grodansparadis/can4vscp_kelvin_ntc10k/docs/save/modules_kelvin_sht [VSCP].pdf

## KelYin SHT

## DoZnload

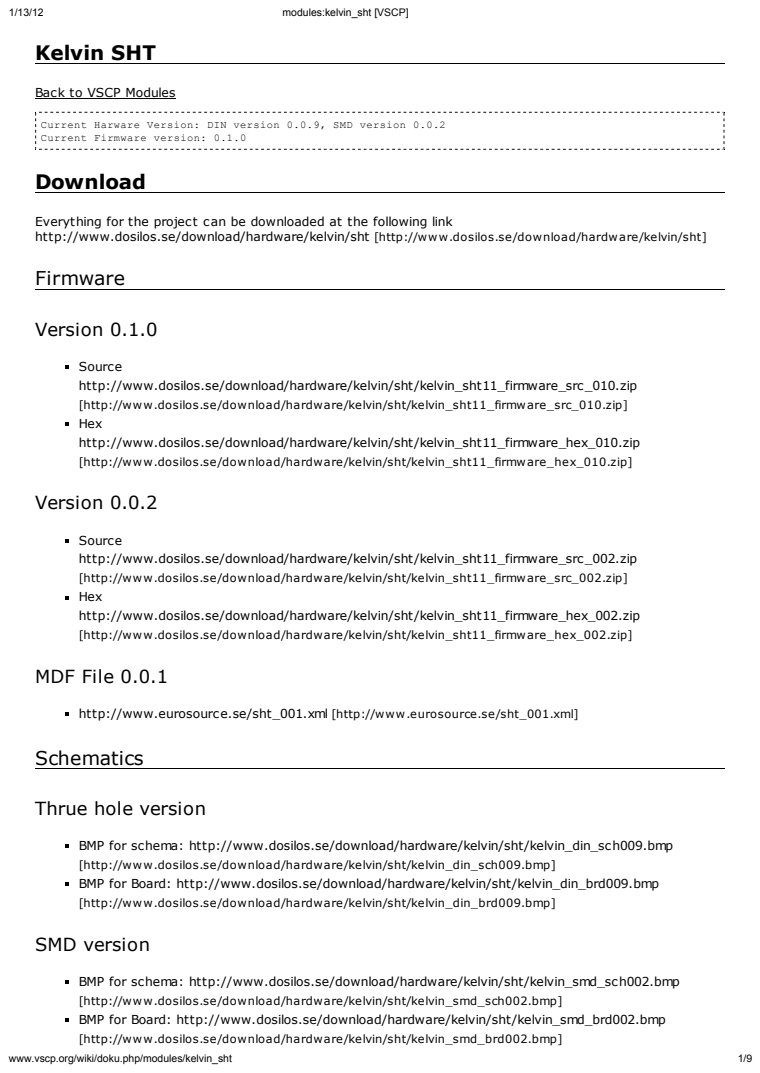
[picture p13: page 1]
modXleV:kelYin_VhW [VSCP]; ZZZ.YVcp.oUg/Ziki/dokX.php/modXleV/kelYin_VhW; VeUVion 0.1.0

Back Wo VSCP ModXleV

EYeU\Whing foU Whe pUojecW can be doZnloaded aW Whe folloZing link
hWWp://ZZZ.doViloV.Ve/doZnload/haUdZaUe/kelYin/VhW [hWWp://ZZZ.doViloV.Ve/doZnload/haUdZaUe/kelYin/VhW]
FiUmZaUe

SoXUce
hWWp://ZZZ.doViloV.Ve/doZnload/haUdZaUe/kelYin/VhW/kelYin_VhW11_fiUmZaUe_VUc_010.]ip
[hWWp://ZZZ.doViloV.Ve/doZnload/haUdZaUe/kelYin/VhW/kelYin_VhW11_fiUmZaUe_VUc_010.]ip]
hWWp://ZZZ.doViloV.Ve/doZnload/haUdZaUe/kelYin/VhW/kelYin_VhW11_fiUmZaUe_he[_010.]ip
[hWWp://ZZZ.doViloV.Ve/doZnload/haUdZaUe/kelYin/VhW/kelYin_VhW11_fiUmZaUe_he[_010.]ip]
VeUVion 0.0.2

hWWp://ZZZ.doViloV.Ve/doZnload/haUdZaUe/kelYin/VhW/kelYin_VhW11_fiUmZaUe_VUc_002.]ip
[hWWp://ZZZ.doViloV.Ve/doZnload/haUdZaUe/kelYin/VhW/kelYin_VhW11_fiUmZaUe_VUc_002.]ip]
hWWp://ZZZ.doViloV.Ve/doZnload/haUdZaUe/kelYin/VhW/kelYin_VhW11_fiUmZaUe_he[_002.]ip
[hWWp://ZZZ.doViloV.Ve/doZnload/haUdZaUe/kelYin/VhW/kelYin_VhW11_fiUmZaUe_he[_002.]ip]
MDF File 0.0.1

hWWp://ZZZ.eXUoVoXUce.Ve/VhW_001.[ml [hWWp://ZZZ.eXUoVoXUce.Ve/VhW_001.[ml]
SchemaWicV

ThUXe hole YeUVion

BMP foU Vchema: hWWp://ZZZ.doViloV.Ve/doZnload/haUdZaUe/kelYin/VhW/kelYin_din_Vch009.bmp
[hWWp://ZZZ.doViloV.Ve/doZnload/haUdZaUe/kelYin/VhW/kelYin_din_Vch009.bmp]
BMP foU BoaUd: hWWp://ZZZ.doViloV.Ve/doZnload/haUdZaUe/kelYin/VhW/kelYin_din_bUd009.bmp
[hWWp://ZZZ.doViloV.Ve/doZnload/haUdZaUe/kelYin/VhW/kelYin_din_bUd009.bmp]
SMD YeUVion

BMP foU Vchema: hWWp://ZZZ.doViloV.Ve/doZnload/haUdZaUe/kelYin/VhW/kelYin_Vmd_Vch002.bmp
[hWWp://ZZZ.doViloV.Ve/doZnload/haUdZaUe/kelYin/VhW/kelYin_Vmd_Vch002.bmp]
BMP foU BoaUd: hWWp://ZZZ.doViloV.Ve/doZnload/haUdZaUe/kelYin/VhW/kelYin_Vmd_bUd002.bmp
[hWWp://ZZZ.doViloV.Ve/doZnload/haUdZaUe/kelYin/VhW/kelYin_Vmd_bUd002.bmp]

## AboXW

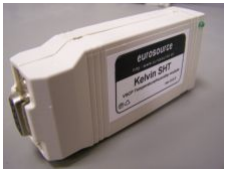
[picture p14: figure]

Control module

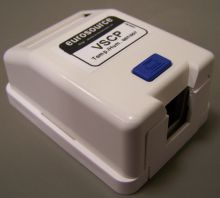
[picture p15: figure]

Sensor module

The Kelvin SHT module is an open hardware/software temperature and humidity module for the VSCP (Very Simple Control Protocol) for use over CAN (Controller Area Network). The module is mounted in a DIN norm box with standard one unit width (17.5 mm ) or in a small case that can be used on or off a DIN rail.

The module is built around a Microchip PIC18F248/PIC18F2480 and the code is written in C using the Microchip MCC-18 compiler.

The Kelvin SHT can be powered with 9-16V DC and draws about 0.15W.

Kelvin SHT is also available in the form of a bare PCB. Firmware, electronic drawings and PCB layout are freely available and can be freely used in both commercial and non commercial projects.

The module, the PCB and components for it can be bought from eurosource at http://www.eurosource.se[http://www.eurosource.se] In its default configuration the module sends out temperature, humidity and dew-point events once every 30 seconds. The interval as well as the format for the data can be customized. Currently temperature and dew-point can be reported in Kelvin, Celsius and Fahrenheit.

The module can be configured to send out alarm events on high/low temperature/humidity.

The module keeps track of absolute min/max values and also has a running mean for all values.

The temperature data is accurate to +- 0.4 degree at 25 degrees Celsius and is typically +-2 over the sensors entire range. The Humidity data is accurate to +- 3% and reported dew-point typically has a +-1 degree accuracy. A calibration value can be set in the module for both temperature and humidity but is not needed for normal use.

Temperature range is -40 to +123 degrees Celsius.

## InVWalling

The module have screw connections on two sides. One side is for CAN and power (marked ³CAN + Power´ ) and the other side is for the sensor (marked ³sensor´).

## Connecting the sensor

DATA | CLOCK
+5V | GND

Attach the

orange lead to +5V in the lower left.
orange/white lead to GND in the lower right
blue lead (DATA) to upper left position.
blue/white lead (CLOCK) to the upper right position.

## Connecting CAN and Power

CANH | CANL
9-16V DC | GND

Attach CANL to the upper right position and CANH to the upper left position. If this is the first or the last module in the chain set the 120 ohm terminator (a standard 120 ohms resistor) between CANL and CANH.

CAT5 twisted pair cable should be used and there should be less than 100 meters between the first and the last node. Both ends of the bus should be terminated with a 120 ohm resistor (coupled between CANL and CANH).

Connect the ground cable from the bus to the ground position in the lower right position.

and Power«

First turn of the power source. You should never connect a module with power on.

Secondl\ \ou have to decide if the module should be powered from the bus or from a local power source.

If powered from the bus just connect the power line to the lower left screw terminal. Connect ground to lower right position.

If \ou have a local DC power source is should be between 9-16V. Connect the positive side to the lower left screw terminal and ground to the lower right screw terminal.

Depending on which modules \ou have installed \ou can power about 50 modules from the bus if 16V is used.

Your module is now read\ for some real work.

## Starting it up

When the module is first powered up the green lamp starts to blink to indicate that the module is uninitiali]ed. Press the red button on the device. The address negotiation now starts. The lamp will stop blinking and light stead\ when initiali]ed or be turned of if an error occurs It is important to understand as VSCP over CAN requires at least two modules on the bus to be working. If \ou have a computer CAN interface this is counted as one node. The interface should be open and the CAN bitrate set to 500 kbps.

## Registers

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

R e g i V W e U 6 ( 0 [ 0 6 ) C X U U e n W d e Z p o i n W , M S B . R e a d o n l \ .
R e g i V W e U 7 ( 0 [ 0 7 ) C X U U e n W d e Z p o i n W , L S B . R e a d o n l \ .

R e g i V W e U 8 ( 0 [ 0 8 ) A b V o l X W e h i g h W e m p e U a W X U e , M S B . R e a d / W U i W e . R e g i V W e U 9 ( 0 [ 0 9 ) A b V o l X W e h i g h W e m p e U a W X U e , L S B . R e a d / W U i W e .

Writing an\ value to register 8 or 9 will reset there content.

R e g i V W e U 1 0 ( 0 [ 0 A ) A b V o l X W e l o Z W e m p e U a W X U e , M S B . R e a d / W U i W e . R e g i V W e U 1 1 ( 0 [ 0 B ) A b V o l X W e l o Z W e m p e U a W X U e , L S B . R e a d / W U i W e .

Writing an\ value to register 10 or 11 will reset there content.

R e g i V W e U 1 2 ( 0 [ 0 C ) A b V o l X W e h i g h h X m i d i W \ , M S B . R e a d / W U i W e . R e g i V W e U 1 3 ( 0 [ 0 D ) A b V o l X W e h i g h h X m i d i W \ , M S B . R e a d / W U i W e .

Writing an\ value to register 12 or 13 will reset there content.

R e g i V W e U 1 4 ( 0 [ 0 E ) A b V o l X W e l o Z h X m i d i W \ , M S B . R e a d / W U i W e .
R e g i V W e U 1 5 ( 0 [ 0 F ) A b V o l X W e l o Z h X m i d i W \ , M S B . R e a d / W U i W e .

Writing an\ value to register 14 or 15 will reset there content.

R e g i V W e U 1 6 ( 0 [ 1 0 ) A b V o l X W e h i g h d e Z p o i n W , M S B . R e a d / W U i W e . R e g i V W e U 1 7 ( 0 [ 1 1 ) A b V o l X W e h i g h d e Z p o i n W , L S B . R e a d / W U i W e .

Writing an\ value to register 16 or 17 will reset there content.

R e g i V W e U 1 8 ( 0 [ 1 2 ) A b V o l X W e l o Z d e Z p o i n W , M S B . R e a d / W U i W e . R e g i V W e U 1 9 ( 0 [ 1 3 ) A b V o l X W e l o Z d e Z p o i n W , L S B . R e a d / W U i W e .

Writing an\ value to register 18 or 19 will reset there content.

R e g i V W e U 2 0 ( 0 [ 1 4 ) R X n n i n g m e a n o f W e m p e U a W X U e , M S B . R e a d / W U i W e . R e g i V W e U 2 1 ( 0 [ 1 5 ) R X n n i n g m e a n o f W e m p e U a W X U e , L S B . R e a d / W U i W e .

Writing an\ value to register 20 or 21 will set mean value to ]ero.

R e g i V W e U 2 2 ( 0 [ 1 6 ) R X n n i n g m e a n o f h X m i d i W \ , M S B . R e a d / W U i W e .
R e g i V W e U 2 3 ( 0 [ 1 7 ) R X n n i n g m e a n o f h X m i d i W \ , L S B . R e a d / W U i W e .

Writing an\ value to register 22 or 23 will set mean value to ]ero.

R e g i V W e U 2 4 ( 0 [ 1 8 ) R X n n i n g m e a n o f d e Z p o i n W , M S B . R e a d / W U i W e . R e g i V W e U 2 5 ( [ 0 1 9 ) R X n n i n g m e a n o f d e Z p o i n W , L S B . R e a d / W U i W e .

Writing an\ value to register 24 or 25 will set mean value to ]ero.

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

R e g i V W e U 3 0 ( 0 [ 1 E ) T e m p e U a W X U e V e n V o U U e a d e U U o U c o X n W e U . R e a d / W U i W e .
A Z U i W e o f a n \ Y a l X e V e W W h e U e g i V W e U W o ] e U o .

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

All values, temperature, humidity, dew point are stored as 100 * the real value. This is to preserve two decimals as they are stored as integers. This means that you should divide a read value with 100 to get the real value. This is true for all registers except for the alarm points.

## Alarm register

You can read standard VSCP register 128 (0î80) to get alarm status for the device. When an alarm is generated the corresponding bit in the alarm register will be set. The bit will be cleared by a read of the alarm register .You can therefore pick up alarm conditions without looking for alarm events.

This can also be used as a safeguard against missed alarm events.

Bit | Description
Bit 7 | Temperature high alarm.
Bit 6 | Temperature low alarm.
Bit 5 | Humidity high alarm.
Bit 4 | Humidity low alarm.
Bit 3 | Reserved.
Bit 2 | Reserved.
Bit 1 | Reserved.
Bit 0 | Reserved.

## EYents

The following events are generated by this device.

## Temperature Event

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

The temperature is reported as a normalized integer value by this event. The event frequency is set in register 33 (0î21) (default is one event per 30 seconds). Set this register to zero to disable the event.

Temperature can be reported in one of three units. Kelvin, Celsius (default) or Fahrenheit as set in register 36 (0î24).

C l a s s : 0 [ 0 0 A
T \ p e : 0 [ 0 6

Format:

See below.

Package:

B\te | Description
Byte 0 | format
Byte 1 | 0î02 (exponent)
Byte 2 | MSB of normalized integer
Byte 3 | LSB of normalized integer

format is the measurement data coding format described in the VSCP specification

Bits | Description
5,6,7 | 0î08 - Normalized integer format.
3,4 | 0î00 - Kelvin 0î01 – Celsius 0î02 – Fahrenheit.
0,1,2 | Sendor Index: 0î00 or 0î01 for sensor 1 or sensor 2.
Package examples

+40.00 degrees Celsius is reported as:

B\te | Description
Byte 0 | 0î88
Byte 1 | 0î02
Byte 2 | 0x0F
Byte 3 | 0xA0

+120.00 degrees Celsius is reported as:

B\te | Description
Byte 0 | 0î88
Byte 1 | 0î02
Byte 2 | 0x2E
Byte 3 | 0xE0

0.00 degrees Celsius is reported as:

B\te | Description
Byte 0 | 0î88
Byte 1 | 0î02
Byte 2 | 0î00
Byte 3 | 0î00

-40.00 degrees Celsius is reported as:

B\te | Description
Byte 0 | 0î88
Byte 1 | 0î02
Byte 2 | 0xF0

Byte 3 0î60
1.38 degrees Celsius is reported as:
B\te | Description
Byte 0 | 0î88
Byte 1 | 0î02
Byte 2 | 0î00
Byte 3 | 0x8A

## Humidity

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

The humidity is reported as a floating point value by this event. The event frequency is set in register 34 (0î22) (default one event per 30 seconds). Set this register to zero to disable the event.

Humidity is always reported in percent (0-100%).

For most nodes which are low level devices floating point is not the preferred data format. This is not a problem as the data can be read in byte 2 (MSB) and byte (3(LSB) as a value 100 times the measured value. The sign for this value can be fetched from bit 7 of byte 2.

C l a s s 0 [ 0 0 A
T \ p e 0 [ 2 3

Format:

See below.

Package:

B\te | Description
Byte 0 | 0î80
Byte 1 | 0î02 (exponent)
Byte 2 | MSB of normalized integer
Byte 3 | LSB of normalized integer

format is the measurement data coding format described in the VSCP specification

Bits | Description
Bits 5,6,7 0î08 | Normalized integer format.
Bits 3,4 0î00 | Realative humidity.
Bits 1,2,3 | 0î00 or 0î01 for sensor 1 or sensor 2.
Package examples

47.54% humidity is reported as:

B\te | Description
Byte 0 | 0î80
Byte 1 | 0î02
Byte 2 | 0î12
Byte 3 | 0î92

## Dew point

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

The calculated dew point is reported as a normalized integer value by this event. The event frequency is set in register 35 (0î23) (default one event per 30 seconds). Set this register to zero to disable the event. Dew point can be reported in one of three units. Kelvin, Celsius (default) and Fahrenheit as set in register 36

(0î24).

C l a s s 0 [ 0 0 A
T \ p e 0 [ 3 1

Format:

See below.

Package:

B\te | Description
Byte 0 | format
Byte 1 | 0î02 (exponent)
Byte 2 | MSB of normalized integer
Byte 3 | LSB of normalized integer

format is the measurement data coding format described in the VSCP specification

Bits | Description
Bits 5,6,7 | 0î08 - Normalized integer format.
Bits 3,4 | 0î00 - Kelvin 0î01 – Celsius 0î02 – Fahrenheit.
Bits 1,2,3 | 0î00 or 0î01 for sensor 1 or sensor 2.

## Alarm

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

The module can send alarm events on a number of conditions:

Temperature over limit (code = 1).
Temperature under limit (code = 2).
Humidity over limit (code = 3).
Humidity under limit (code = 4).

Code = 0 is reserved for a general alarm and is not used at the moment.

One event will be sent for each alarm type generated. When the corresponding alarm flag is set in the alarm register set after an alarm no new alarms will be generated until the bit is cleared and a new alarm condition occurs.

C l a s s 0 [ 0 0 1
T \ p e 0 [ 0 2

Format:

none

Package:

B\te | Description
Byte 0 | code for alarm type.
Byte 1 | Alarm register.

## Error

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

An error message is sent out if a failure is detected with the module or the SHT-xx sensor.

Error code = 0 – Reserved
Error code = 1 – Sensor fault. Error code = 2 – Module fault.

C l a V V : 0 [ 0 1 4
T \ p e : 0 [ 0 d

Format:

none

Package:

B\te | Description
Byte 0 | error code.

## Contact Information

This is open hardware / software that is made by Ake Hedman, eurosource, Sweden. It is free to use for commecial or non commercial use.

Email: vscp@eurosource.se [mailto:vscp@eurosource.se]

Company:

e X U o V o X U c e
B U a W W b e U g a Y a g e n 1 7 8 2 0 5 0 L O S
S W E D E N

i n f o @ e X U o V o X U c e . V e
h W W p : / / Z Z Z . e X U o V o X U c e . V e

P h o n e : + 4 6 6 5 7 4 1 3 4 3 0
F a [ : + 4 6 6 5 7 4 1 3 5 0 3

Modules and components are sold at http://www.eurosource.se/catalog [http://www.eurosource.se/catalog]

More info about the VSCP and CANAL protocol can be found at http://www.vscp.org [http://www.vscp.org]

module, can, climate

modules /kelvin_sht.txt Las t modified: 2011/01/03 08:44 by admin
