grodansparadis/can4vscp_kelvin_ntc10k/docs/save/modules_kelvin_smart_ii [VSCP].pdf

## Kelvin Smart II - dual temperature module

## Download

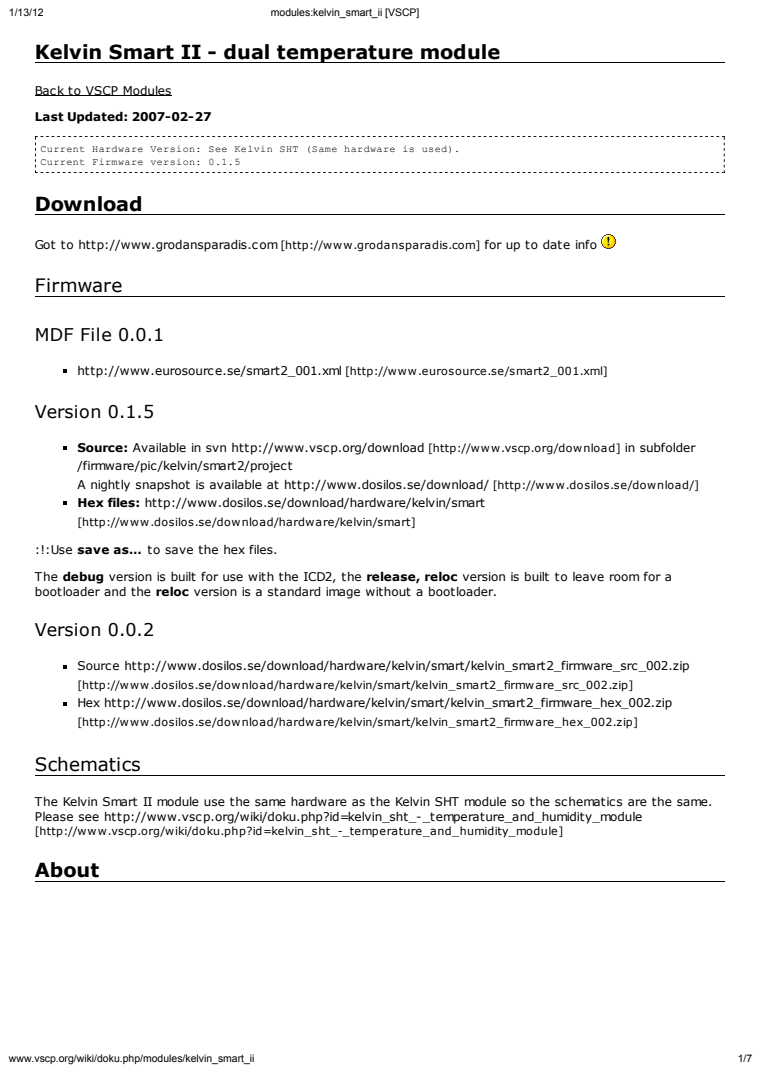
[picture p16: page 1]
modXleV:kelYin_VmaUW_ii [VSCP]; ZZZ.YVcp.oUg/Ziki/dokX.php/modXleV/kelYin_VmaUW_ii; MDF File 0.0.1

Back Wo VSCP ModXleV
Last Updated: 2007-02-27

GoW Wo hWWp://ZZZ.gUodanVpaUadiV.com [hWWp://ZZZ.gUodanVpaUadiV.com] foU Xp Wo daWe info
FiUmZaUe

hWWp://ZZZ.eXUoVoXUce.Ve/VmaUW2_001.[ml [hWWp://ZZZ.eXUoVoXUce.Ve/VmaUW2_001.[ml]
VeUVion 0.1.5

Source: AYailable in VYn hWWp://ZZZ.YVcp.oUg/doZnload [hWWp://ZZZ.YVcp.oUg/doZnload] in VXbfoldeU
/fiUmZaUe/pic/kelYin/VmaUW2/pUojecW
A nighWl\ VnapVhoW iV aYailable aW hWWp://ZZZ.doViloV.Ve/doZnload/ [hWWp://ZZZ.doViloV.Ve/doZnload/]
Hex files: hWWp://ZZZ.doViloV.Ve/doZnload/haUdZaUe/kelYin/VmaUW
[hWWp://ZZZ.doViloV.Ve/doZnload/haUdZaUe/kelYin/VmaUW]

:!:UVe save as« Wo VaYe Whe he[ fileV.
The debug YeUVion iV bXilW foU XVe ZiWh Whe ICD2, Whe release, reloc YeUVion iV bXilW Wo leaYe Uoom foU a
booWloadeU and Whe reloc YeUVion iV a VWandaUd image ZiWhoXW a booWloadeU.
VeUVion 0.0.2

SoXUce hWWp://ZZZ.doViloV.Ve/doZnload/haUdZaUe/kelYin/VmaUW/kelYin_VmaUW2_fiUmZaUe_VUc_002.]ip
[hWWp://ZZZ.doViloV.Ve/doZnload/haUdZaUe/kelYin/VmaUW/kelYin_VmaUW2_fiUmZaUe_VUc_002.]ip]
He[ hWWp://ZZZ.doViloV.Ve/doZnload/haUdZaUe/kelYin/VmaUW/kelYin_VmaUW2_fiUmZaUe_he[_002.]ip
[hWWp://ZZZ.doViloV.Ve/doZnload/haUdZaUe/kelYin/VmaUW/kelYin_VmaUW2_fiUmZaUe_he[_002.]ip]
SchemaWicV

The KelYin SmaUW II modXle XVe Whe Vame haUdZaUe aV Whe KelYin SHT modXle Vo Whe VchemaWicV aUe Whe Vame.
PleaVe Vee hWWp://ZZZ.YVcp.oUg/Ziki/dokX.php?id=kelYin_VhW_-_WempeUaWXUe_and_hXmidiW\_modXle
[hWWp://ZZZ.YVcp.oUg/Ziki/dokX.php?id=kelYin_VhW_-_WempeUaWXUe_and_hXmidiW\_modXle]
About

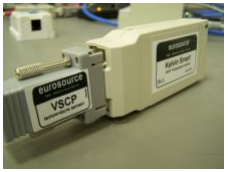
[picture p17: figure]

The Kelvin Smart II module is an open hardware and software temperature times two module for the VSCP (Very Simple Control Protocol) for use over CAN (Controller Area Network). The module is mounted in a DIN norm box with standard one unit width (17.5 mm ) Two sensors can be connected to the module using cables with up to 20 meters length.

The module is built around a Microchip PIC 18F258/PIC18F2580 and the open source code is written in C using the Microchip MCC-18 compiler.

The Kelvin Smart II can be powered with 9-16V DC and draws about 0.15W.

Kelvin Smart II is also available in the form of a bare PCB. Firmware, electronic drawings and PCB layout are freely available and can be freely used in both commercial and non commercial projects.

The module, the PCB and components for it can be bought at http://www.eurosource.se[http://www.eurosource.se] In its default configuration the module sends out temperature events for each of its sensors once every 30 seconds. The interval as well as the format for the data can be customized. Currently temperature can be reported in Kelvin, Celsius and Fahrenheit.

The module can be configured to send out alarm events on high/low temperature.

The module keeps track of absolute min/max values and also has a running mean for all values.

The temperature data is accurate to +- 0.7 degree at 25 degrees Celsius and is typically +-1.2 over the sensors entire range. A calibration value can be set in the module for both temperature and humidity but is not needed for normal use.

Working temperature range for the module is -45 to +130 degrees Celsius.

Read\ built modules and sensors can be bought here http://www.eurosource.se/catalog[http://www.eurosource.se/catalog]

## Description

The Kelvin Smart II module is an open hardware and software temperature module for the VSCP (Very Simple Control Protocol) for use over CAN (Controller Area Network). The module is mounted in a DIN norm box with standard one unit width (17.5 mm ) The module is built around a Microchip PIC18F258/PIC18F2580 and the code is written in C using the Microchip MCC-18 compiler.

The Kelvin Smart II can be powered with 9-16V DC and draws about 0.15W.

## Installing

The module have screw connections on two sides. One side is for CAN and power (marked ³CAN + Power´ ) and the other side is for the sensor (marked ³sensor´).

## Connecting the sensor

Sensor 1 | Sensor 2
+5V | GND

Attach the

Power lead of sensor to +5V in the lower left.

GND lead of sensor to GND in the lower right Sensor 1 to upper left screw terminal. Sensor 2 to upper right screw terminal.

## Connecting CAN and Power

CANH | CANL
9-16V DC | GND

Attach CANL to the upper right position and CANH to the upper left position. If this is the first or the last module in the chain set the 120 ohm terminator (a standard 120 ohms resistor) between CANL and CANH.

CAT5 twisted pair cable should be used and there should be less than 500 meters between the first and the last node. Both ends of the bus should be terminated with a 120 ohm resistor (coupled between CANL and CANH).

Connect the ground cable from the bus to the ground position in the lower right position.

and power«

First \ou have to decide if the module should be powered from the bus or from a local power source.

If powered from the bus just connect the power line to the lower left screw terminal. Connect ground to lower right position.

If \ou have a local DC power source is should be between 9-16V. Connect the positive side to the lower left screw terminal and ground to the lower right screw terminal.

Depending on which modules \ou have installed \ou can power about 50 modules from the bus if 16V is used.

Your module is now read\ for some real work.

## Starting it up

When the module is first powered up the green lamp starts to blink to indicate that the module is uninitiali]ed. Press the red button on the device. The address negotiation now starts. The lamp will stop blinking and light stead\ when initiali]ed or be turned of if an error occurs

It is important to understand as VSCP over CAN requires at least two modules on the bus to be working. If \ou have a computer CAN interface this is counted as one node. The interface should be open and the CAN bitrate set to 125 kbps.

## Registers

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

Writing an\ value to register 8 or 9 will reset there content.

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

Writing an\ value to register 8 or 9 will reset there content.

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

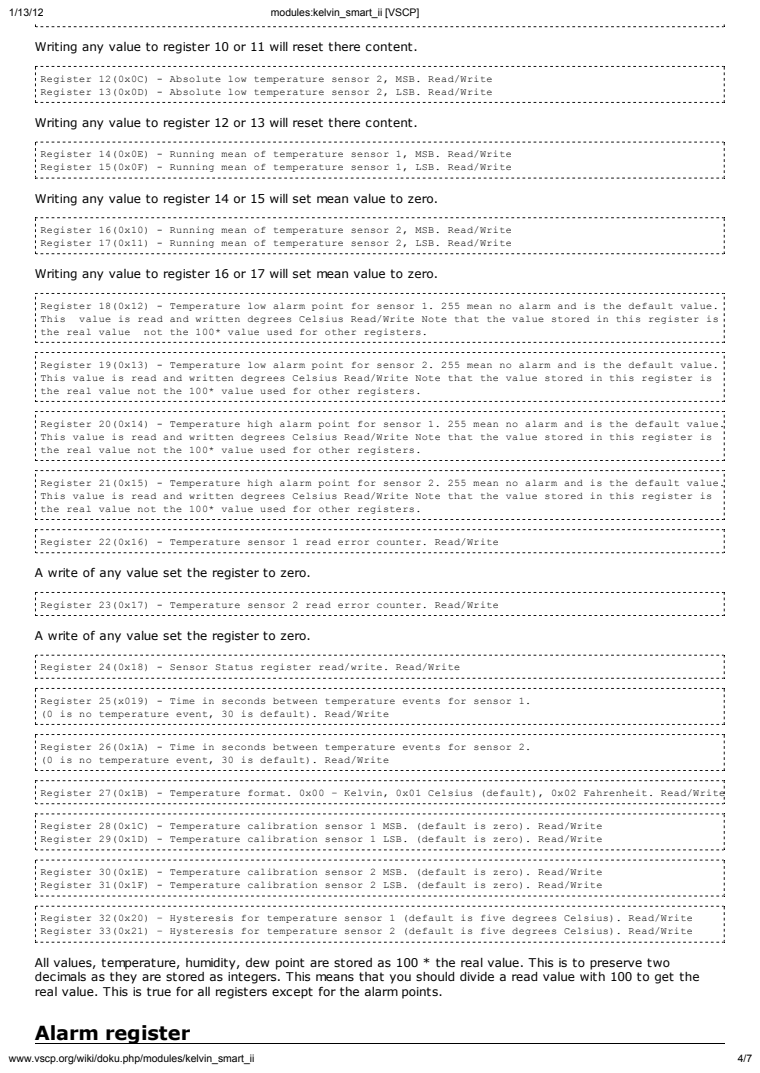
[picture p18: page 4]

WUiWing an\ YalXe Wo UegiVWeU 10 oU 11 Zill UeVeW WheUe conWenW.

WUiWing an\ YalXe Wo UegiVWeU 12 oU 13 Zill UeVeW WheUe conWenW.

WUiWing an\ YalXe Wo UegiVWeU 14 oU 15 Zill VeW mean YalXe Wo ]eUo.

WUiWing an\ YalXe Wo UegiVWeU 16 oU 17 Zill VeW mean YalXe Wo ]eUo.

A ZUiWe of an\ YalXe VeW Whe UegiVWeU Wo ]eUo.

All YalXeV, WempeUaWXUe, hXmidiW\, deZ poinW aUe VWoUed aV 100 * Whe Ueal YalXe. ThiV iV Wo pUeVeUYe WZo
decimalV aV Whe\ aUe VWoUed aV inWegeUV. ThiV meanV WhaW \oX VhoXld diYide a Uead YalXe ZiWh 100 Wo geW Whe
Ueal YalXe. ThiV iV WUXe foU all UegiVWeUV e[cepW foU Whe alaUm poinWV.
AlaUm UegiVWeU

You can read standard VSCP register 128 (0î80) to get alarm status for the device. When an alarm is generated the corresponding bit in the alarm register will be set. The bit will be cleared by a read of the alarm register .You can therefore pick up alarm conditions without looking for alarm events.

This can also be used as a safeguard against missed alarm events.

Bits | Description
Bit 7 | Temperature high alarm.
Bit 6 | Temperature low alarm.
Bit 5 | Reserved.
Bit 4 | Reserved.
Bit 3 | Reserved.
Bit 2 | Reserved.
Bit 1 | Reserved.
Bit 0 | Reserved.

## Events

The following events are generated by this device.

## Temperature

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

The temperature is reported as a normalized integer value by this event. The event frequency for sensor 1 is set in register 25 (0î19) and for sensor 2 in register 26 (0x1A) (default is one event per 30 seconds). Set register to zero to disable the event for one or both sensors.

Temperature can be reported in one of three units. Kelvin, Celsius (default) and Fahrenheit as set in register 36 (0î24).

For most other nodes which are low level devices floating point is not the preferred data format. This is not a problem as the data can be read in byte 4 (MSB) and byte (5(LSB) as a value 100 times the measured value. The sign for this value can be fetched from bit 7 of byte 2.

C l a s s : 0 [ 0 0 A
T \ p e : 0 [ 0 6

Package:

B\te | Description
Byte 0 | format.
Byte 1 | 0î02 (exponent).
Byte 2 | LSB of normalized integer.
Byte 3 | MSB of normalized integer.
Format:

See below.

format is the measurement data coding format described in the VSCP specification

Bits | Description
Bits 5,6,7 | 0î04 Normalized integer format.
Bits 3,4 | 0î00 == Kelvin Celsius == 0î01 Fahrenheit == 0î02
Bits 0,1,2 | Index for sensor. 0î00 or 0î01 for sensor 1 or sensor 2.
Package examples

+40.00 degrees Celsius from sensor 1 is reported as:

B\te | Description
Byte 0 | 0î88

Byte 1 | 0î02
Byte 2 | 0x0F
Byte 3 | 0xA0

+120.00 degrees Celsius for sensor 2 is reported as:

B\te | Description
Byte 0 | 0î89
Byte 1 | 0î02
Byte 2 | 0x2E
Byte 3 | 0xE0

0.00 degrees Celsius for sensor 2 is reported as:

B\te | Description
Byte 0 | 0î89
Byte 1 | 0î02
Byte 2 | 0î00
Byte 3 | 0î00

-40 degrees Celsius for sensor 1 is reported as:

B\te | Description
Byte 0 | 0î88
Byte 1 | 0î02
Byte 2 | 0xFE
Byte 3 | 0î70

1.38 degrees Celsius for sensor 1 is reported as:

B\te | Description
Byte 0 | 0î88
Byte 1 | 0î02
Byte 2 | 0î00
Byte 3 | 0x8A
Output when no sensors are connected or sensor failure

If no sensors is connected the following data is received from the module

8 9 8 2 8 0 0 0

this value will never show in any other case (represents minus 128 degrees).

## Alarm

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

The module can send alarm events on a number of conditions:

Temperature over limit (code = 1).
Temperature under limit (code = 2).

Code = 0 is reserved for a general alarm and is not used at the moment. One event will be sent for each alarm type generated. When the corresponding alarm flag is set in the alarm register set after an alarm no new alarms will be generated until the bit is cleared and a new alarm condition occurs.

C l a s s : 0 [ 0 0 1
T \ p e : 0 [ 0 2

Format:

none

## Error

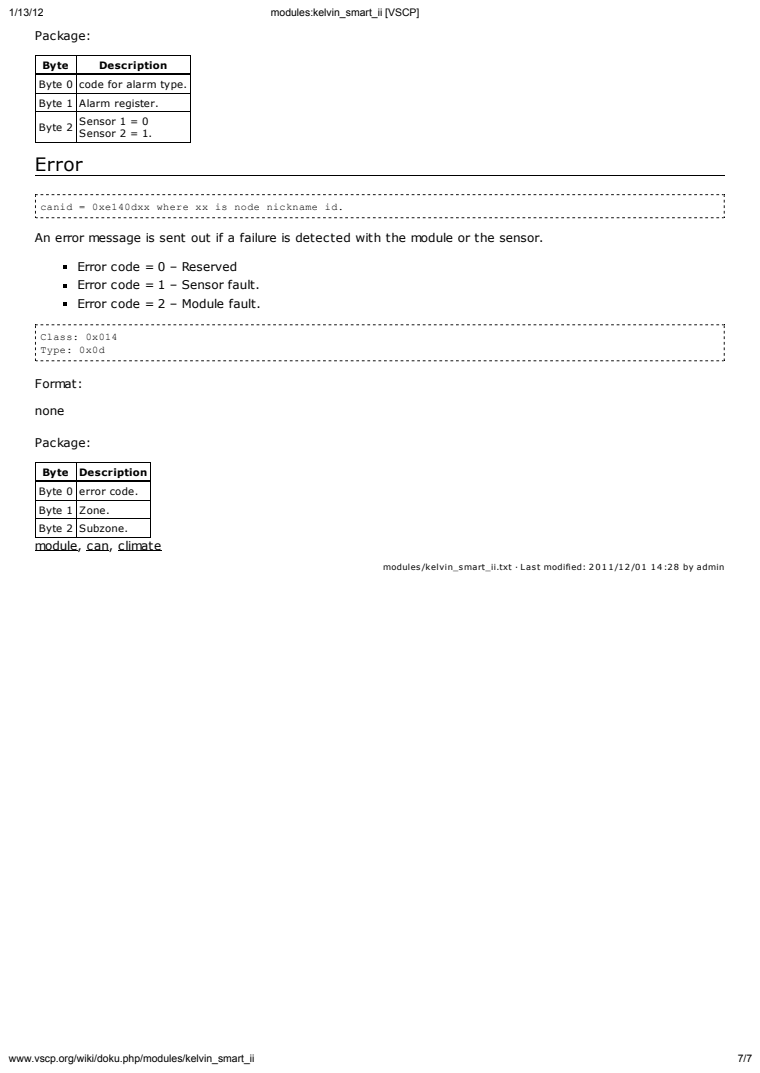
[picture p19: page 7]
Package:; Format:; none

B\te | Description
Byte 0 | code for alarm type.
Byte 1 | Alarm register.
Byte 2 | Sensor 1 = 0 Sensor 2 = 1.

An error message is sent out if a failure is detected with the module or the sensor.

Error code = 0 – Reserved
Error code = 1 – Sensor fault.
Error code = 2 – Module fault.

Byte 0 | error code.
Byte 1 | Zone.
Byte 2 | Subzone.

module, can, climate

modules /kelvin_smart_ii.txt  Las t modified: 2011/12/01 14:28 by admin
