grodansparadis/can4vscp_kelvin_ntc10k/docs/manual-old/_coverpage.md

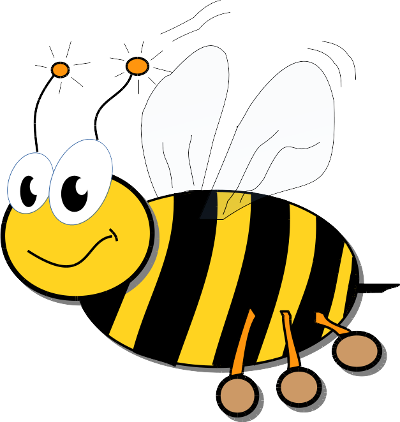
[picture p49: docs/manual-old/images/logo_400.png]
VSCP logo


# CAN4VSCP Kelvin NTC10K module

Scroll down to view docs.

[Homepage](https://www.vscp.org)
[Docs](https://www.vscp.org/#documentation)
[Downloads](https://www.vscp.org/#download)
[Get Started](./README)
