grodansparadis/can4vscp_kelvin_ntc10k/manual/wiki/data/cache/1/1a6f61f85df8579f29ef11f90f4e7916.media.500x375.jpg

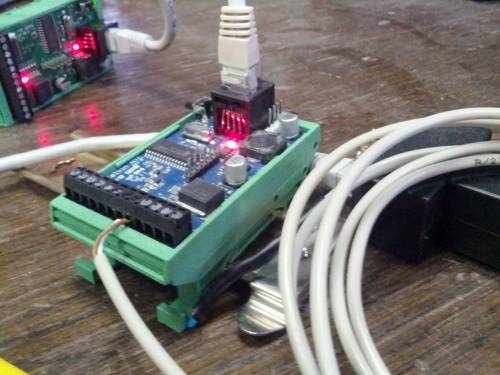
manual/wiki/data/cache/1/1a6f61f85df8579f29ef11f90f4e7916.media.500x375.jpg
