grodansparadis/can4vscp_kelvin_ntc10k/manual/wiki/data/cache/1/1198ec23345d481628cc79729118e7ea.media.700x476.png

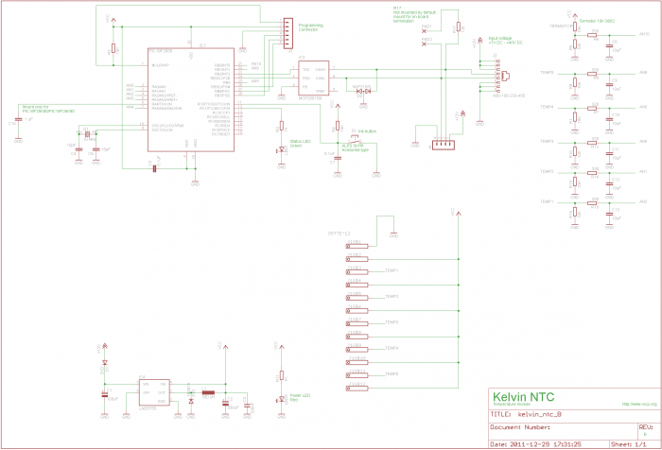
manual/wiki/data/cache/1/1198ec23345d481628cc79729118e7ea.media.700x476.png
