grodansparadis/can4vscp_kelvin_ntc10k/manual/wiki/data/cache/2/2b0202f1f3789b51a12723b0106f13fb.media.880x598.crop.png

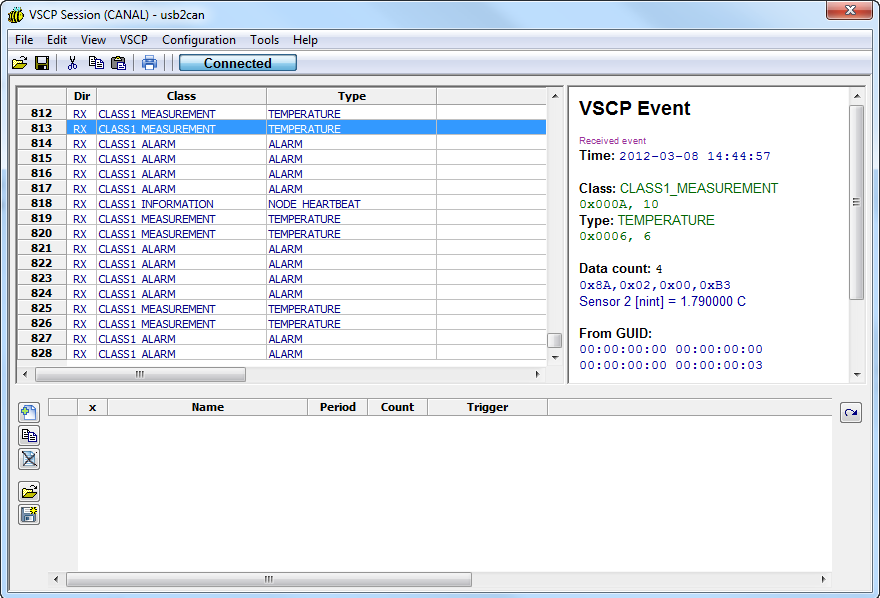
manual/wiki/data/cache/2/2b0202f1f3789b51a12723b0106f13fb.media.880x598.crop.png
