grodansparadis/can4vscp_kelvin_ntc10k/manual/wiki/data/cache/2/2d5771e0f9bb95f86d8358b28fecc915.media.1038x815.crop.png

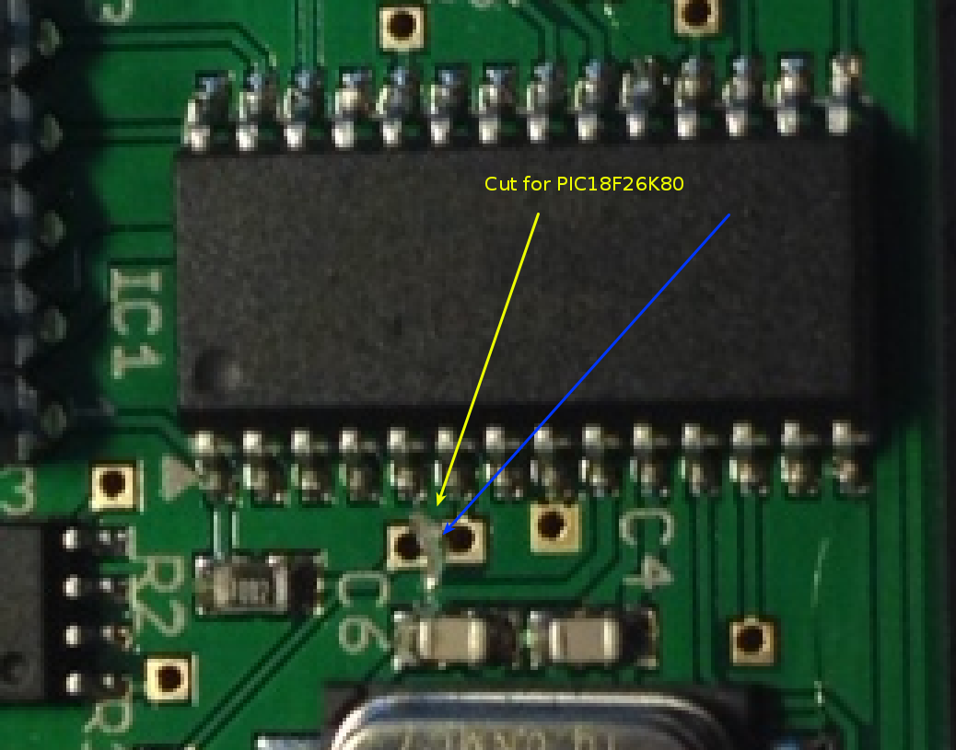
manual/wiki/data/cache/2/2d5771e0f9bb95f86d8358b28fecc915.media.1038x815.crop.png
