grodansparadis/can4vscp_kelvin_ntc10k/manual/wiki/data/cache/2/2958ae1e50585f1528c30ca891e6bee4.media.500x222.png

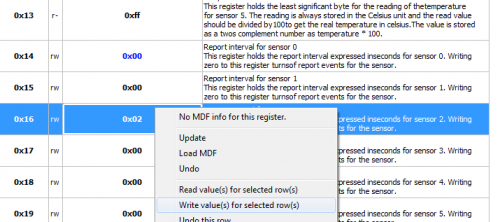
manual/wiki/data/cache/2/2958ae1e50585f1528c30ca891e6bee4.media.500x222.png
