grodansparadis/can4vscp_kelvin_ntc10k/manual/wiki/data/cache/3/33a3dc248a08c98bc5b0178f32b9b613.media.546x275.crop.gif

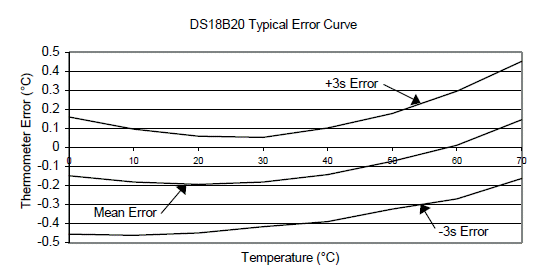
manual/wiki/data/cache/3/33a3dc248a08c98bc5b0178f32b9b613.media.546x275.crop.gif
