grodansparadis/can4vscp_kelvin_ntc10k/manual/wiki/data/cache/4/4dec8ddb7932440de7e6ecd9d4059fe3.media.600x557.png

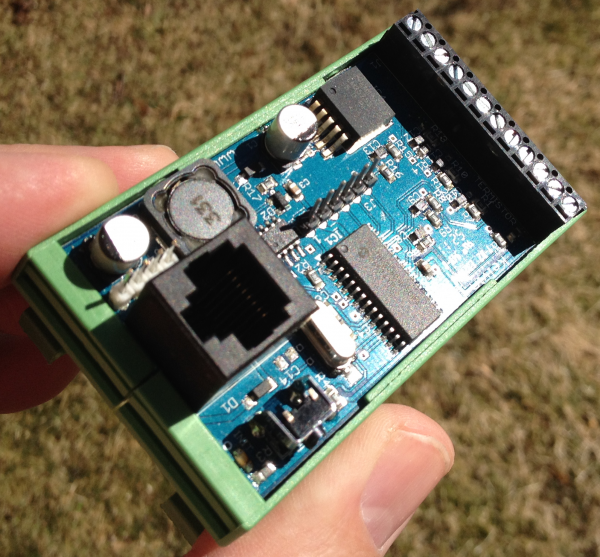
manual/wiki/data/cache/4/4dec8ddb7932440de7e6ecd9d4059fe3.media.600x557.png
