grodansparadis/can4vscp_kelvin_ntc10k/manual/wiki/data/cache/4/4ece00d9c5e9be141f2958b45fc998cf.media.2000x668.crop.png

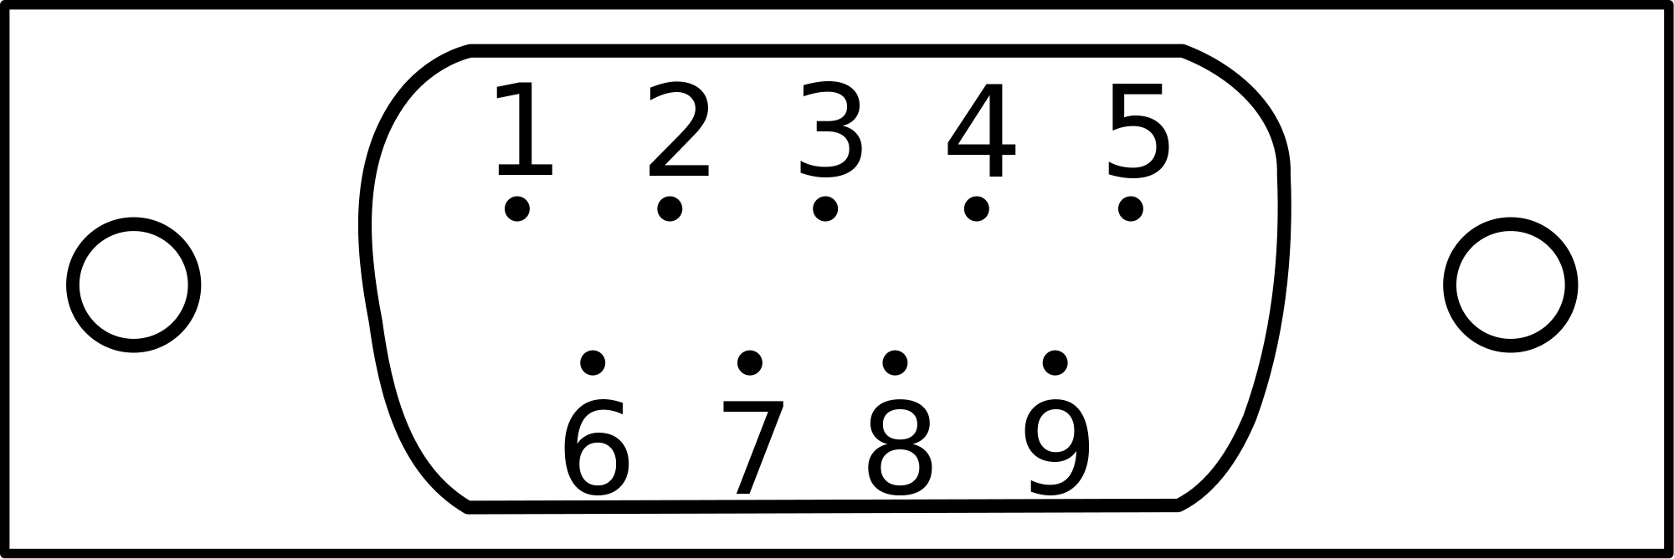
manual/wiki/data/cache/4/4ece00d9c5e9be141f2958b45fc998cf.media.2000x668.crop.png
