grodansparadis/can4vscp_kelvin_ntc10k/manual/wiki/data/cache/5/5b96e2deb4368dbe0f43da134e6f81a7.media.500x194.jpg

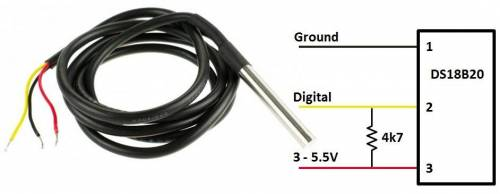
manual/wiki/data/cache/5/5b96e2deb4368dbe0f43da134e6f81a7.media.500x194.jpg
