grodansparadis/can4vscp_kelvin_ntc10k/manual/wiki/data/cache/5/5bdc45c483dae7e3b7d341959cf99819.media.500x394.png

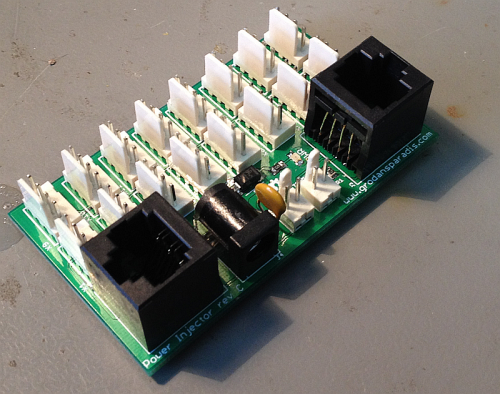
manual/wiki/data/cache/5/5bdc45c483dae7e3b7d341959cf99819.media.500x394.png
