grodansparadis/can4vscp_kelvin_ntc10k/manual/wiki/data/cache/6/6a99e15979a6a93b064ecb7da2fed5aa.media.375x500.jpg

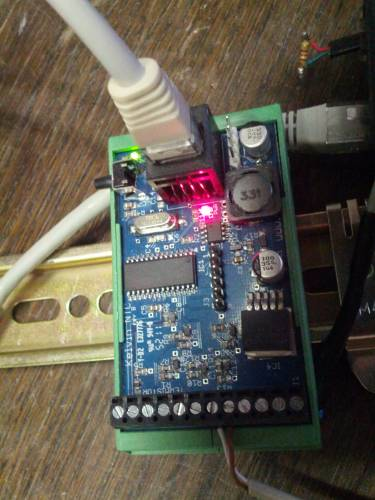
manual/wiki/data/cache/6/6a99e15979a6a93b064ecb7da2fed5aa.media.375x500.jpg
