grodansparadis/can4vscp_kelvin_ntc10k/manual/wiki/data/cache/6/6fe8c004ad2966fe9fa4ecd8705c4d14.media.200x228.png

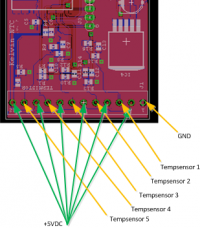
manual/wiki/data/cache/6/6fe8c004ad2966fe9fa4ecd8705c4d14.media.200x228.png
