grodansparadis/can4vscp_kelvin_ntc10k/manual/wiki/data/cache/6/6268c2e0e10d456cecd0ce97f17006b2.media.2510x2714.crop.jpg

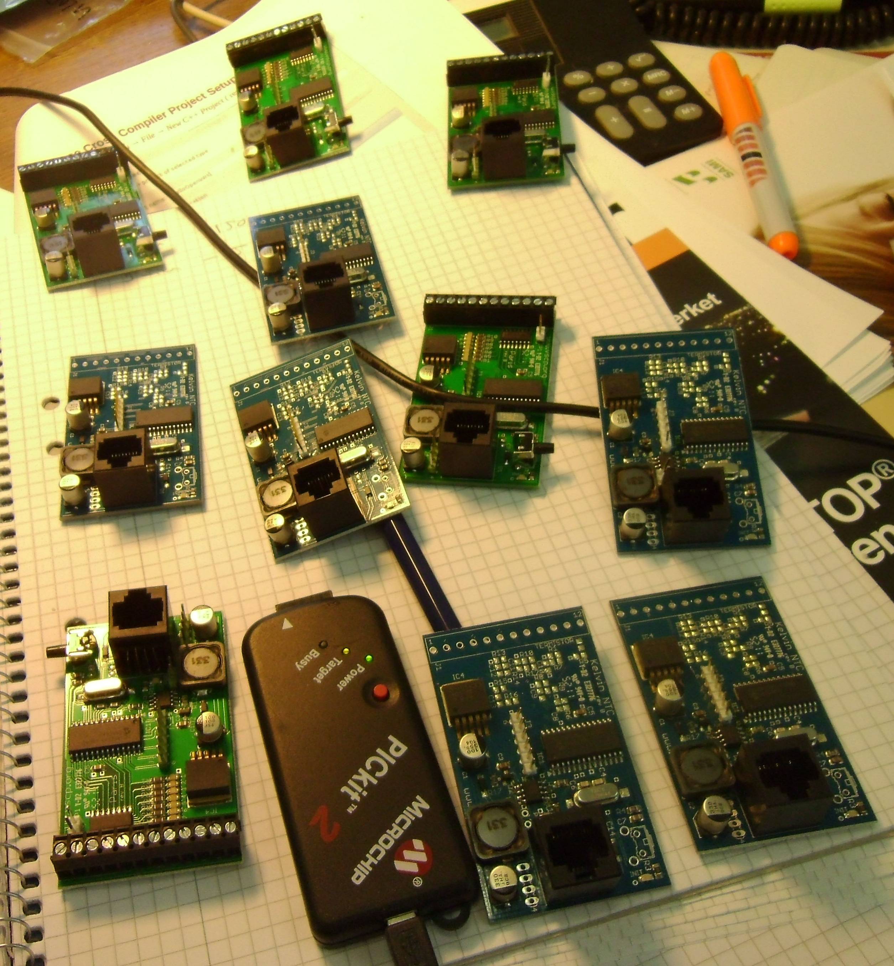
manual/wiki/data/cache/6/6268c2e0e10d456cecd0ce97f17006b2.media.2510x2714.crop.jpg
