grodansparadis/can4vscp_kelvin_ntc10k/manual/wiki/data/cache/6/66049dd03d8fd808455643ebf21cb6ab.media.407x500.png

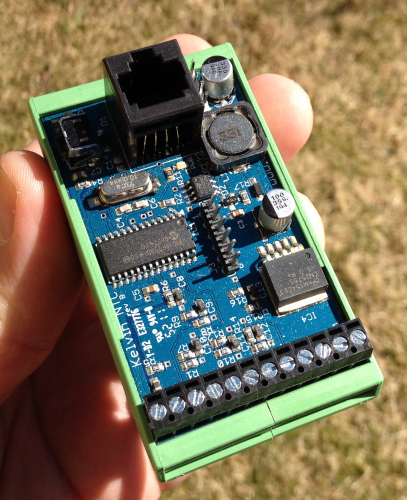
manual/wiki/data/cache/6/66049dd03d8fd808455643ebf21cb6ab.media.407x500.png
