grodansparadis/can4vscp_kelvin_ntc10k/manual/wiki/data/cache/6/67674bd53e3c4fd8513af1146bfd890d.media.120x120.png

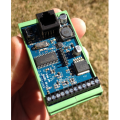
manual/wiki/data/cache/6/67674bd53e3c4fd8513af1146bfd890d.media.120x120.png
