grodansparadis/can4vscp_kelvin_ntc10k/manual/wiki/data/cache/7/7b317a3f38d630d1fc08b12038ab2a5b.media.500x252.gif

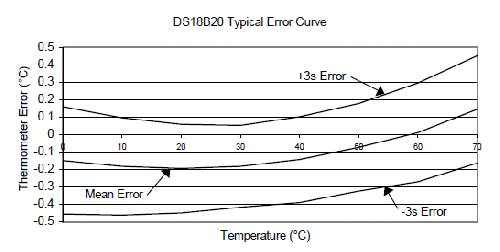
manual/wiki/data/cache/7/7b317a3f38d630d1fc08b12038ab2a5b.media.500x252.gif
