grodansparadis/can4vscp_kelvin_ntc10k/manual/wiki/data/cache/7/7d52a90285c60610a3eb58b0ec5747e6.media.500x375.jpg

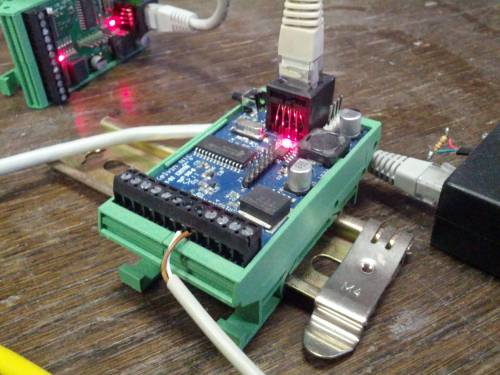
manual/wiki/data/cache/7/7d52a90285c60610a3eb58b0ec5747e6.media.500x375.jpg
