grodansparadis/can4vscp_kelvin_ntc10k/manual/wiki/data/cache/7/788ebb4769704491deb9ed7db11218f9.media.715x315.crop.png

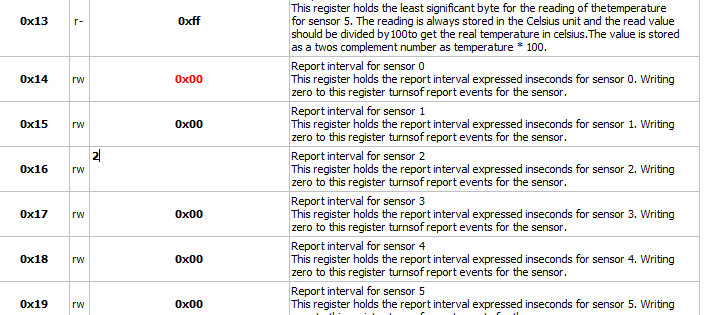
manual/wiki/data/cache/7/788ebb4769704491deb9ed7db11218f9.media.715x315.crop.png
