grodansparadis/can4vscp_kelvin_ntc10k/manual/wiki/data/cache/7/749553fb56f0ec46dcea166d4c9c6214.media.120x120.png

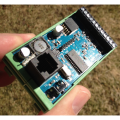
manual/wiki/data/cache/7/749553fb56f0ec46dcea166d4c9c6214.media.120x120.png
