grodansparadis/can4vscp_kelvin_ntc10k/manual/wiki/data/cache/8/8c7404ff7e2337961fa1beaf4dfdae18.media.500x375.jpg

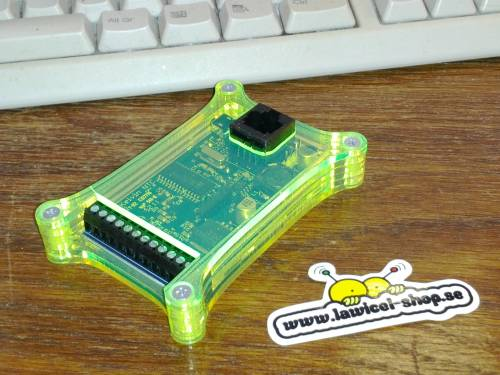
manual/wiki/data/cache/8/8c7404ff7e2337961fa1beaf4dfdae18.media.500x375.jpg
