grodansparadis/can4vscp_kelvin_ntc10k/manual/wiki/data/cache/a/a6ddea56bf01da9688124a576d4b4dce.media.400x358.jpg

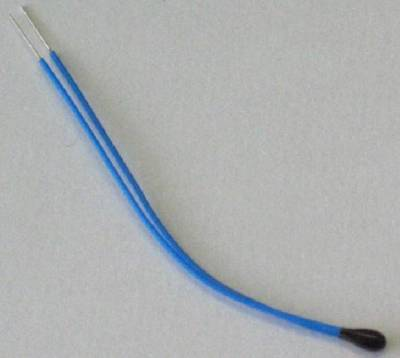
manual/wiki/data/cache/a/a6ddea56bf01da9688124a576d4b4dce.media.400x358.jpg
