grodansparadis/can4vscp_kelvin_ntc10k/manual/wiki/data/cache/a/a99aa1c26bcad66ac0a0a4a9bca1aa86.media.120x120.jpg

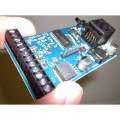
manual/wiki/data/cache/a/a99aa1c26bcad66ac0a0a4a9bca1aa86.media.120x120.jpg
