grodansparadis/can4vscp_kelvin_ntc10k/manual/wiki/data/cache/b/b1de87f94fcb6e3583429863fda920e8.media.500x432.png

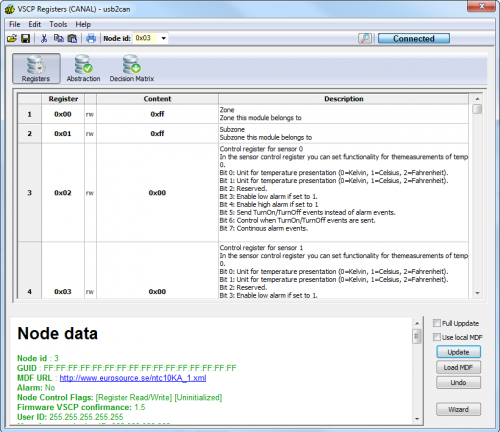
manual/wiki/data/cache/b/b1de87f94fcb6e3583429863fda920e8.media.500x432.png
