grodansparadis/can4vscp_kelvin_ntc10k/manual/wiki/data/cache/b/b44c57620c98f6733b8b2f59034f8f5a.media.500x375.jpg

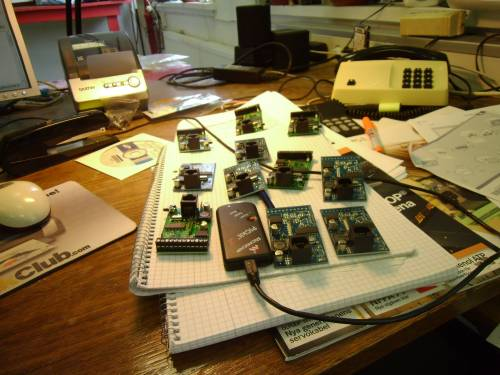
manual/wiki/data/cache/b/b44c57620c98f6733b8b2f59034f8f5a.media.500x375.jpg
