grodansparadis/can4vscp_kelvin_ntc10k/manual/wiki/data/cache/c/c3fc78d1b4575307754465668dc0f781.media.820x708.crop.png

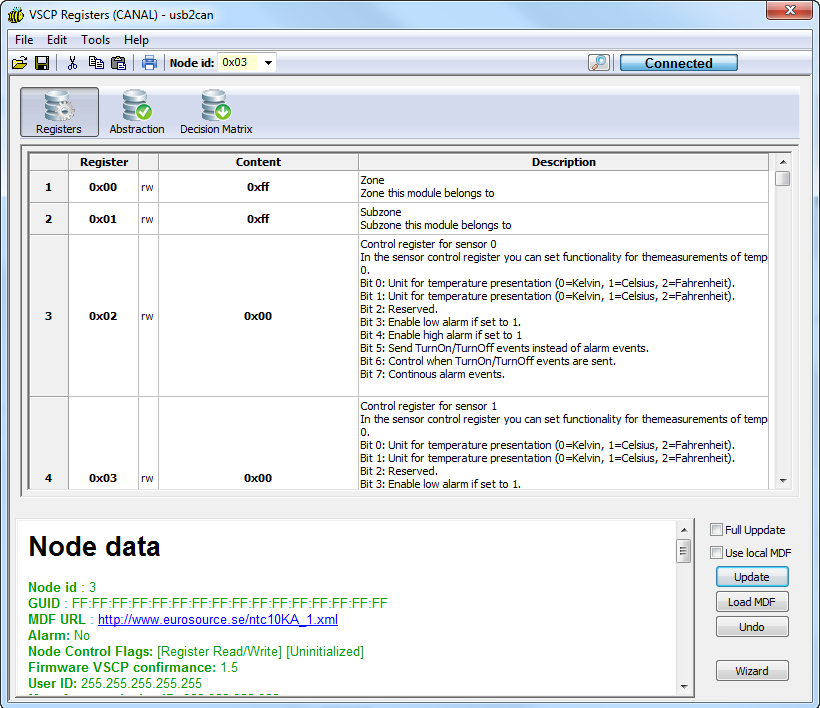
manual/wiki/data/cache/c/c3fc78d1b4575307754465668dc0f781.media.820x708.crop.png
