grodansparadis/can4vscp_kelvin_ntc10k/manual/wiki/data/cache/f/f2cbaf4bf5ef46306333bd0104083c6b.media.715x317.crop.png

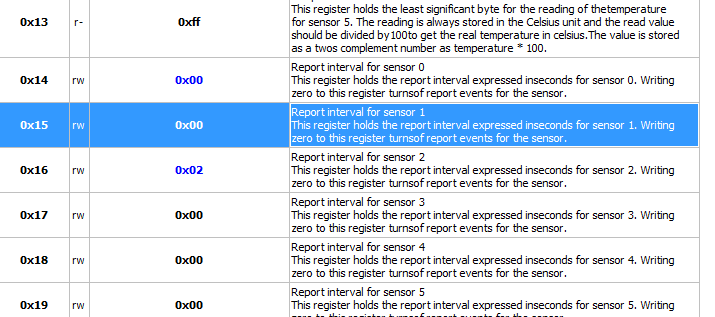
manual/wiki/data/cache/f/f2cbaf4bf5ef46306333bd0104083c6b.media.715x317.crop.png
