grodansparadis/can4vscp_kelvin_ntc10k/docs/manual-old/change_log_1.txt

====== Change Log for Kelvin NTC10K ======

The changelog for firmware can be read [[https://github.com/grodansparadis/can4vscp_kelvin_ntc10k/blob/master/HISTORY.txt|here]].\\ 

===== Documentation changes ======

2016-02-04 AKHE - Page 1 register was not described correctly. Fixed.
2015-06-16 AKHE - Started this change log.

\\ 
---- 
{{ :grodan_logo.png?100 |}}
<html>
<center>
<b>Paradise of the Frog AB</b> Brattbergavägen 17, 820 50 LOS, SWEDEN<br />
<b>email:</b> <a href="info@grodansparadis.com">info@paradiseofthefrog.com</a> <b>phone:</b> +46 (0)8 40011835<br />
<b>web:</b> <a href="http://www.grodansparadis.com">http://www.paradiseofthefrog.com</a><br>
</center>
</html>
