grodansparadis/can4vscp_kelvin_ntc10k/vscp_compiler.h

/* ******************************************************************************
 * 	VSCP (Very Simple Control Protocol) 
 * 	http://www.vscp.org
 *
 *  Copyright (C) 1995-2020 Ake Hedman, eurosource, <akhe@eurosource.se>
 *
 * This software is provided 'as-is', without any express or implied
 * warranty.  In no event will the authors be held liable for any damages
 * arising from the use of this software.
 *
 * Permission is granted to anyone to use this software for any purpose,
 * including commercial applications, and to alter it and redistribute it
 * freely, subject to the following restrictions:
 *
 * 1. The origin of this software must not be misrepresented; you must not
 *    claim that you wrote the original software. If you use this software
 *    in a product, an acknowledgment in the product documentation would be
 *    appreciated but is not required.
 * 2. Altered source versions must be plainly marked as such, and must not be
 *    misrepresented as being the original software.
 * 3. This notice may not be removed or altered from any source distribution.
 * 
 *	This file is part of VSCP - Very Simple Control Protocol 	
 *	http://www.vscp.org
 *
 * ******************************************************************************
*/

#ifndef KELVIN_SMART_COMPILER_H
#define KELVIN_SMART_COMPILER_H





#endif
